thingSoC/TSOC_USBUART2/TSOC_USBUART2/documentation/pinout/TSOC_USBUART2_pinout.pdf

Sheet1

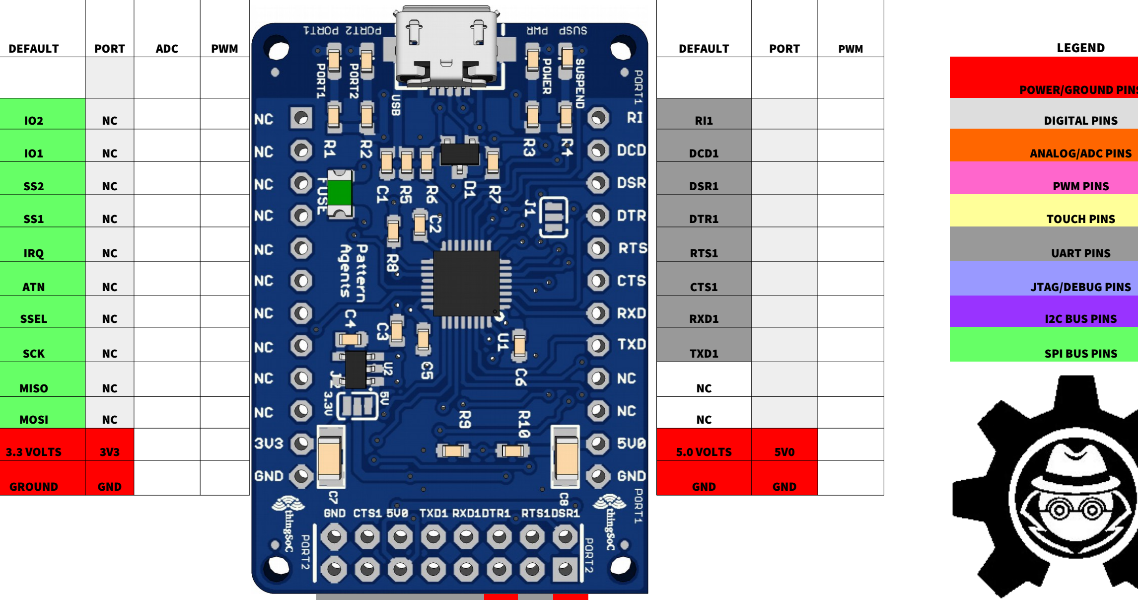
[picture p10: figure]
DIGITAL PINS; DCD1; ANALOG/ADC PINS; DSR1; PWM PINS; DTR1; TOUCH PINS; IRQ; RTS1; UART PINS; ATN; CTS1; JTAG/DEBUG PINS; SSEL; RXD1; I2C BUS PINS; SCK; TXD1; SPI BUS PINS; MISO; MOSI; 3.3 VOLTS; 5.0 VOLTS; GROUND; GND

Page 1

USB

DEFAULT | PORT | ADC | PWM | DEFAULT | PORT | PWM | LEGEND
| | | | | | | POWER/GROUND PINS

DSR2
RTS2

DTR2
TXD2

RXD2
5V0

CTS2
GND

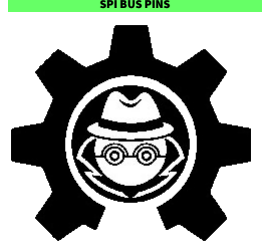
[picture p11: figure]

## PatternAgents thingSoC USBUART2

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
## http://github.com/thingsoc/usbuart2
