thingSoC/TSOC_USBUART2/TSOC_USBUART2/eagleUp/eagleUp_TSOC_USBUART2_board_bottom.jpg

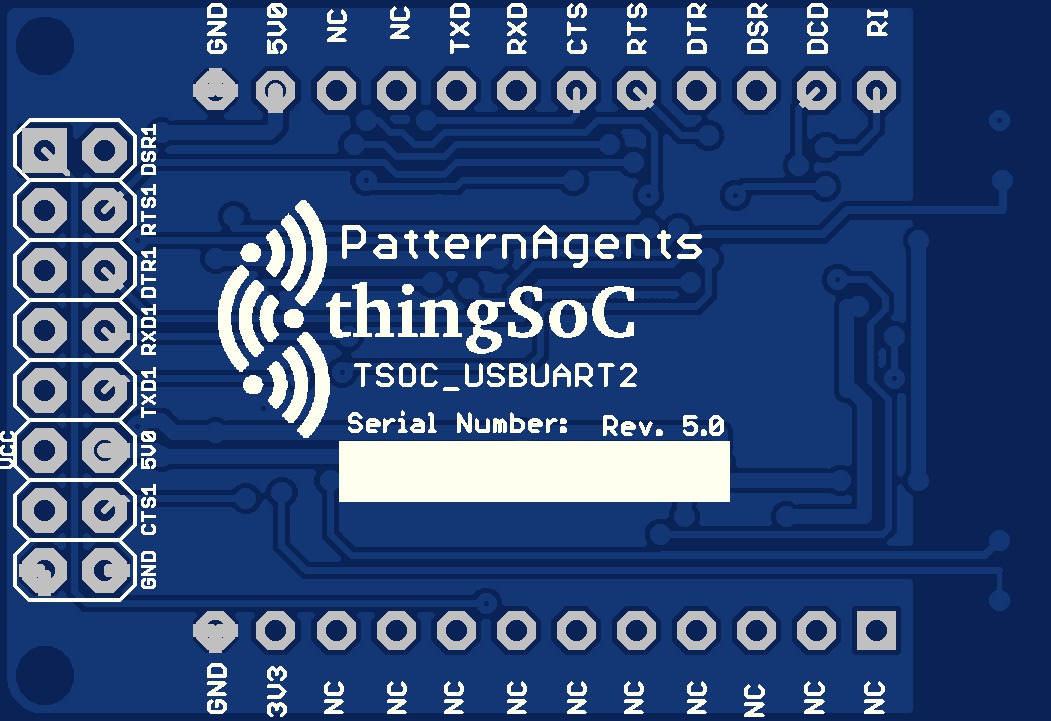
TSOC_USBUART2/eagleUp/eagleUp_TSOC_USBUART2_board_bottom.jpg
