thingSoC/TSOC_USBUART2/TSOC_USBUART2/eagleUp/eagleUp_TSOC_USBUART2_board_top.jpg

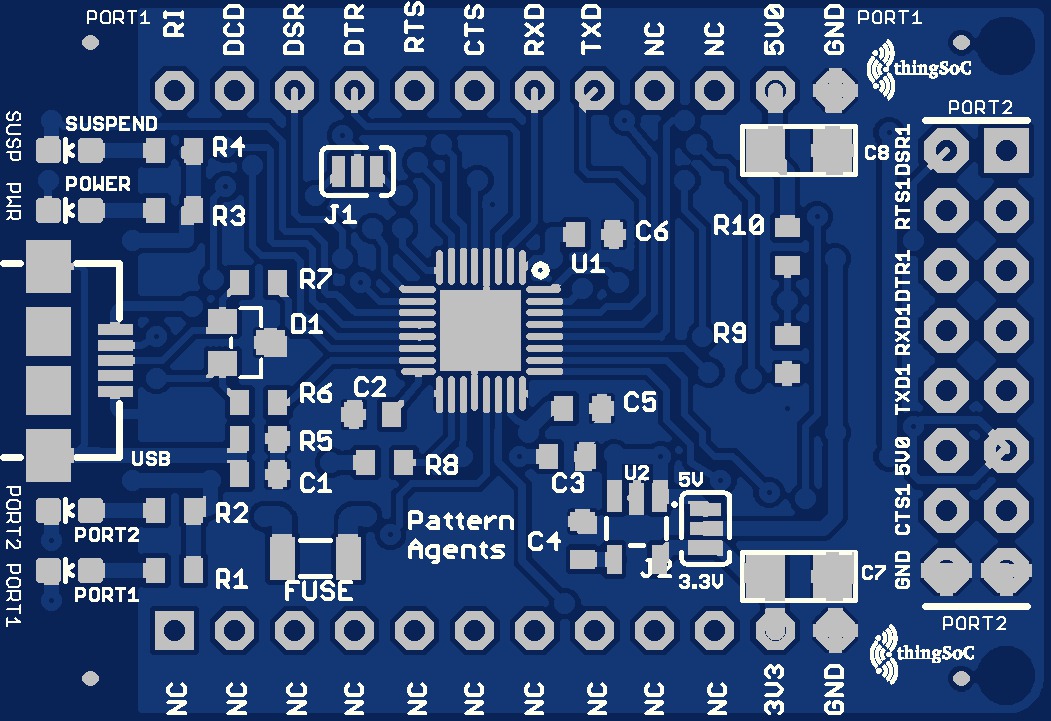
TSOC_USBUART2/eagleUp/eagleUp_TSOC_USBUART2_board_top.jpg
