thingSoC/TSOC_USBUART2/TSOC_USBUART2/images/product/TSOC_UART_top_pop.png

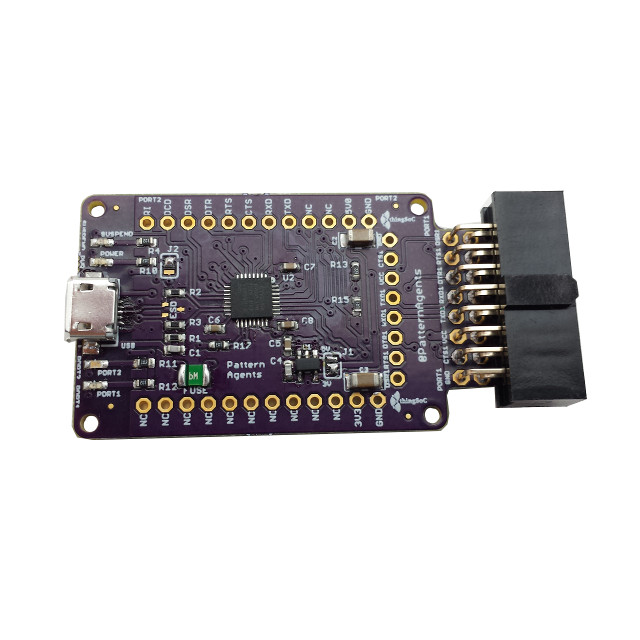
TSOC_USBUART2/images/product/TSOC_UART_top_pop.png
