thingSoC/TSOC_USBUART2/TSOC_USBUART2/images/product/TSOC_USBUART2_adapt_rs485_horiz.jpg

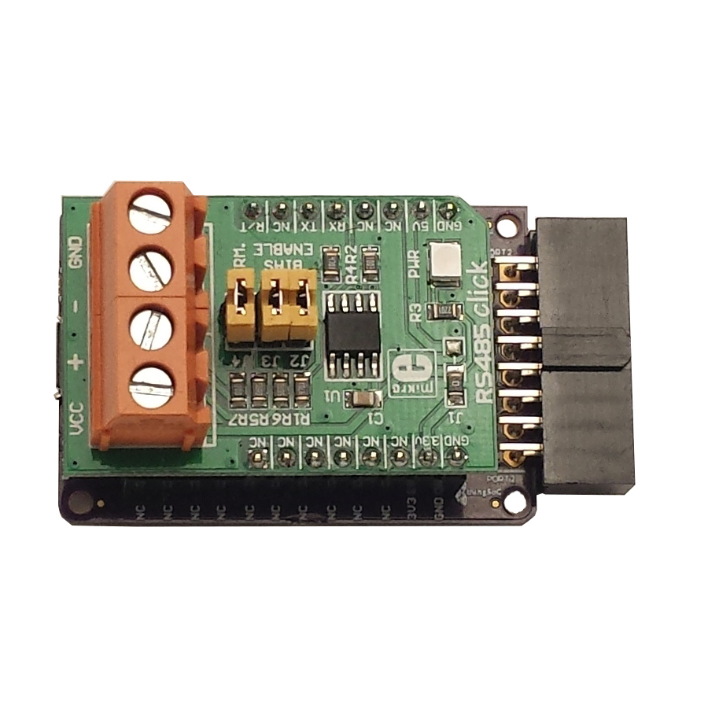
TSOC_USBUART2/images/product/TSOC_USBUART2_adapt_rs485_horiz.jpg
