thingSoC/TSOC_USBUART2/TSOC_USBUART2/images/product/TSOC_USBUART2_bot.png

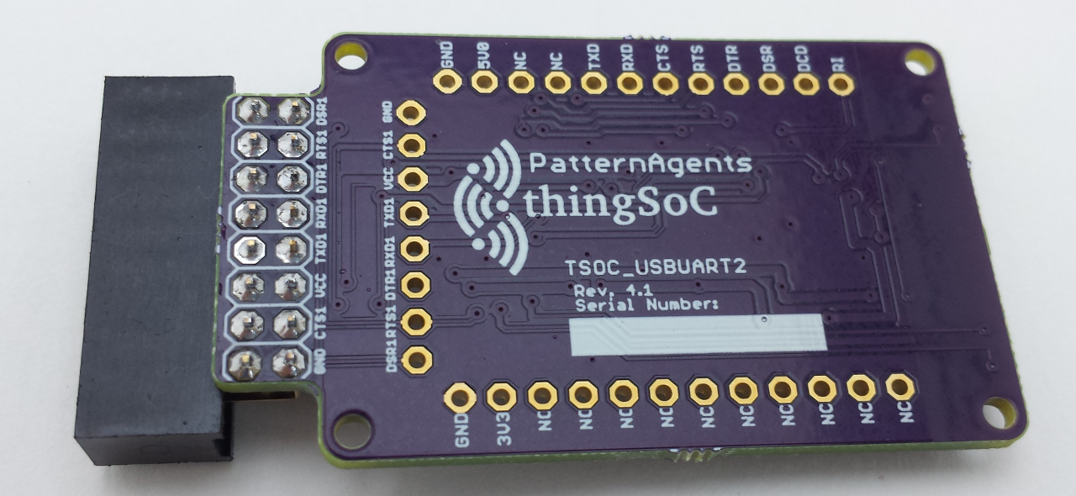
TSOC_USBUART2/images/product/TSOC_USBUART2_bot.png
