thingSoC/TSOC_USBUART2/TSOC_USBUART2/images/product/TSOC_USBUART2_prog_neoled2.png

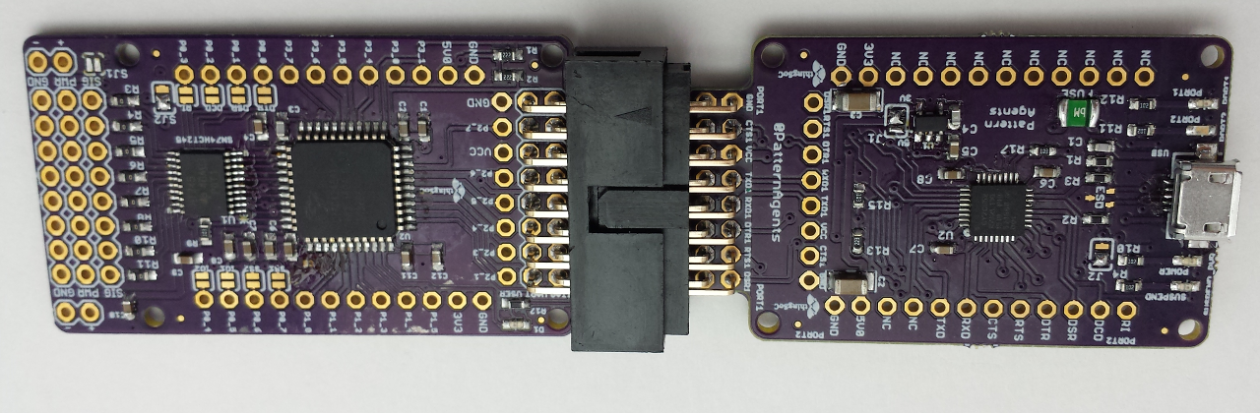
TSOC_USBUART2/images/product/TSOC_USBUART2_prog_neoled2.png
