thingSoC/TSOC_USBUART2/TSOC_USBUART2/images/product/TSOC_USBUART2_rails.png

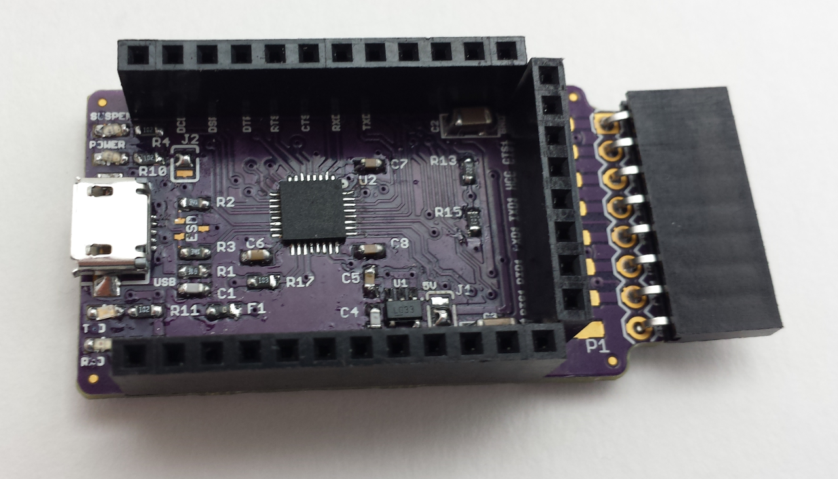
TSOC_USBUART2/images/product/TSOC_USBUART2_rails.png
