thingSoC/TSOC_USBUART2/TSOC_USBUART2/images/product/TSOC_USBUART2_top_pop_sqr.jpg

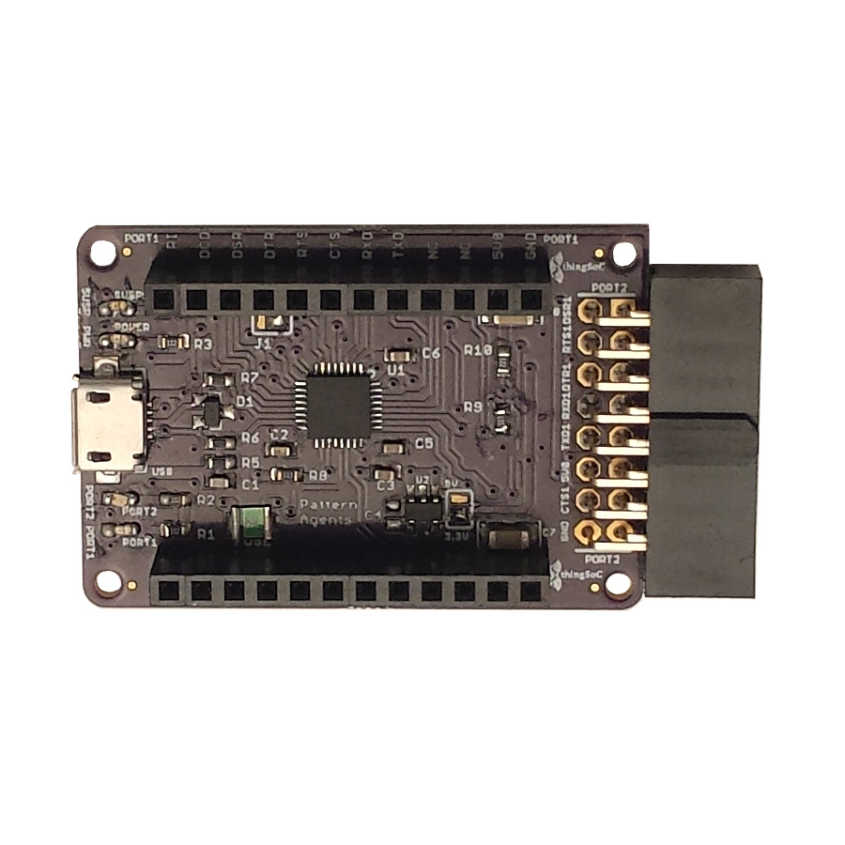
TSOC_USBUART2/images/product/TSOC_USBUART2_top_pop_sqr.jpg
