thingSoC/TSOC_USBUART2/TSOC_USBUART2/images/product/TSOC_USBUART2_with_ESP32S.png

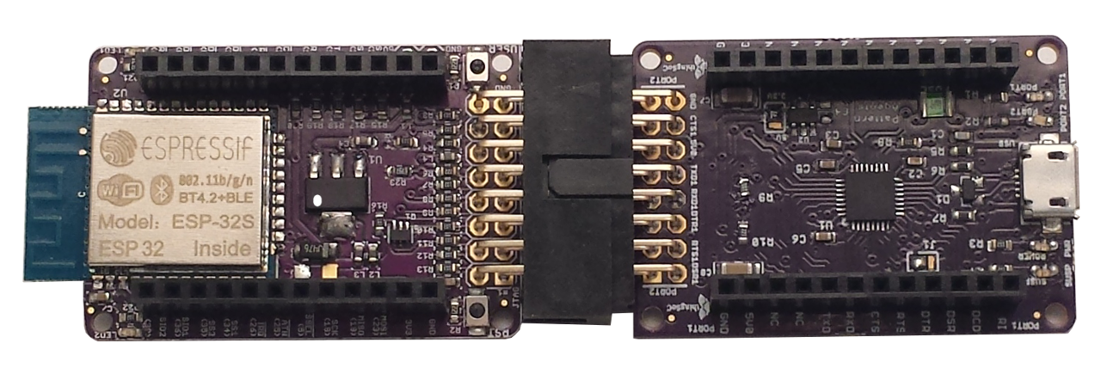
TSOC_USBUART2/images/product/TSOC_USBUART2_with_ESP32S.png
