thingSoC/TSOC_USBUART2/TSOC_USBUART2/images/TSOC_USBUART2.png

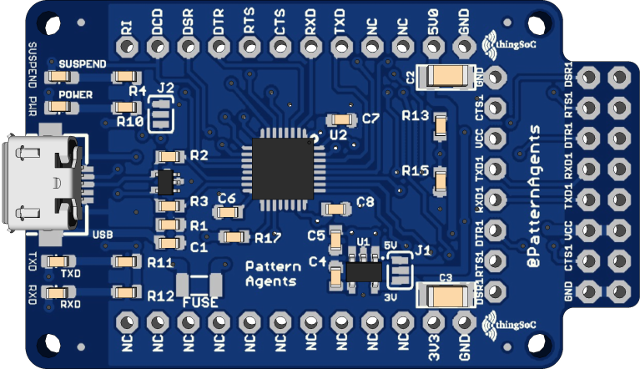
TSOC_USBUART2/images/TSOC_USBUART2.png
