thingSoC/TSOC_USBUART2/TSOC_USBUART2/images/TSOC_USBUART2_iso.png

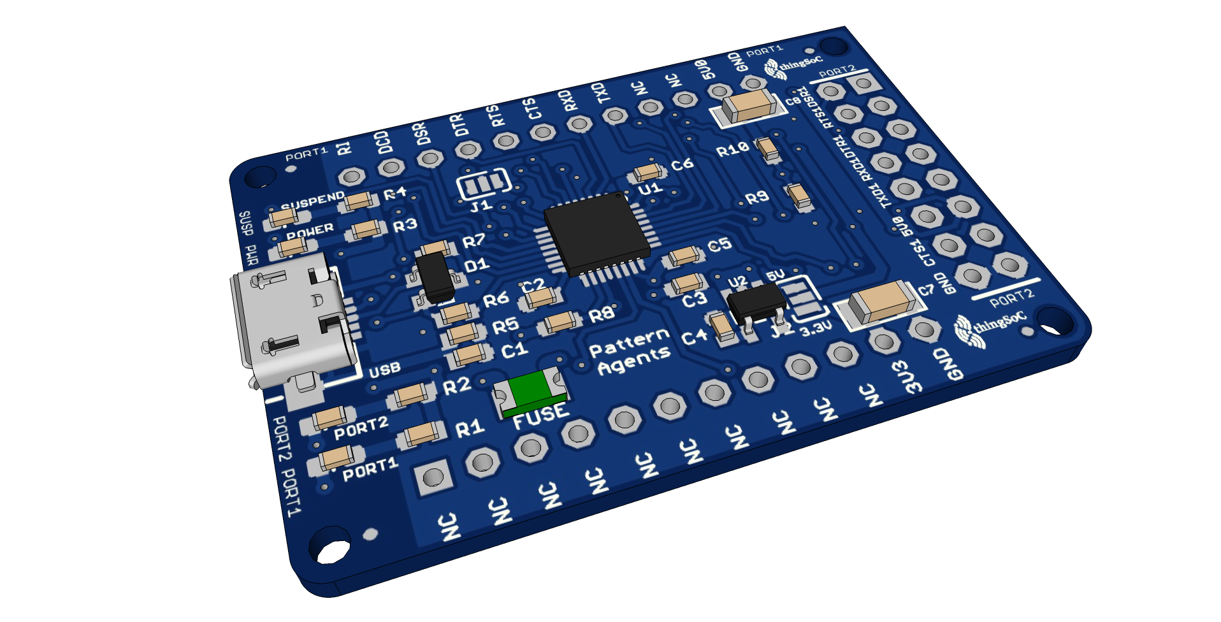
TSOC_USBUART2/images/TSOC_USBUART2_iso.png
