thingSoC/TSOC_USBUART2/TSOC_USBUART2/images/TSOC_USBUART2_top_vert.png

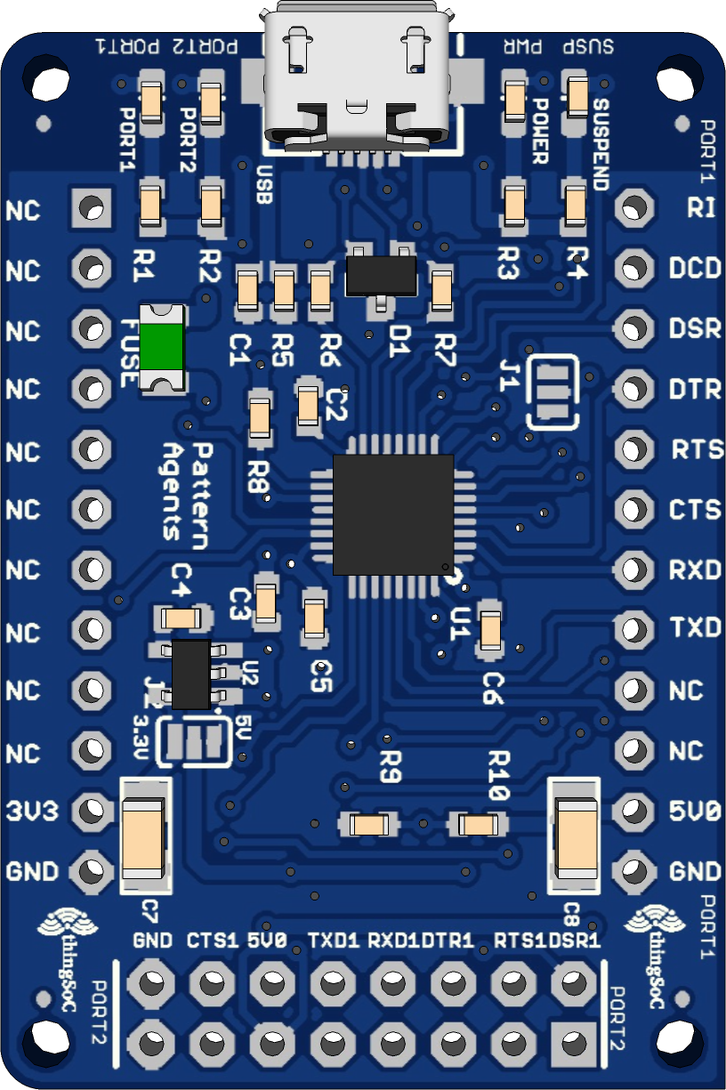
TSOC_USBUART2/images/TSOC_USBUART2_top_vert.png
