thingSoC/TSOC_USBUART2/TSOC_USBUART2/revisions/R4_0/TSOC_USBUART2_sch_blk.pdf

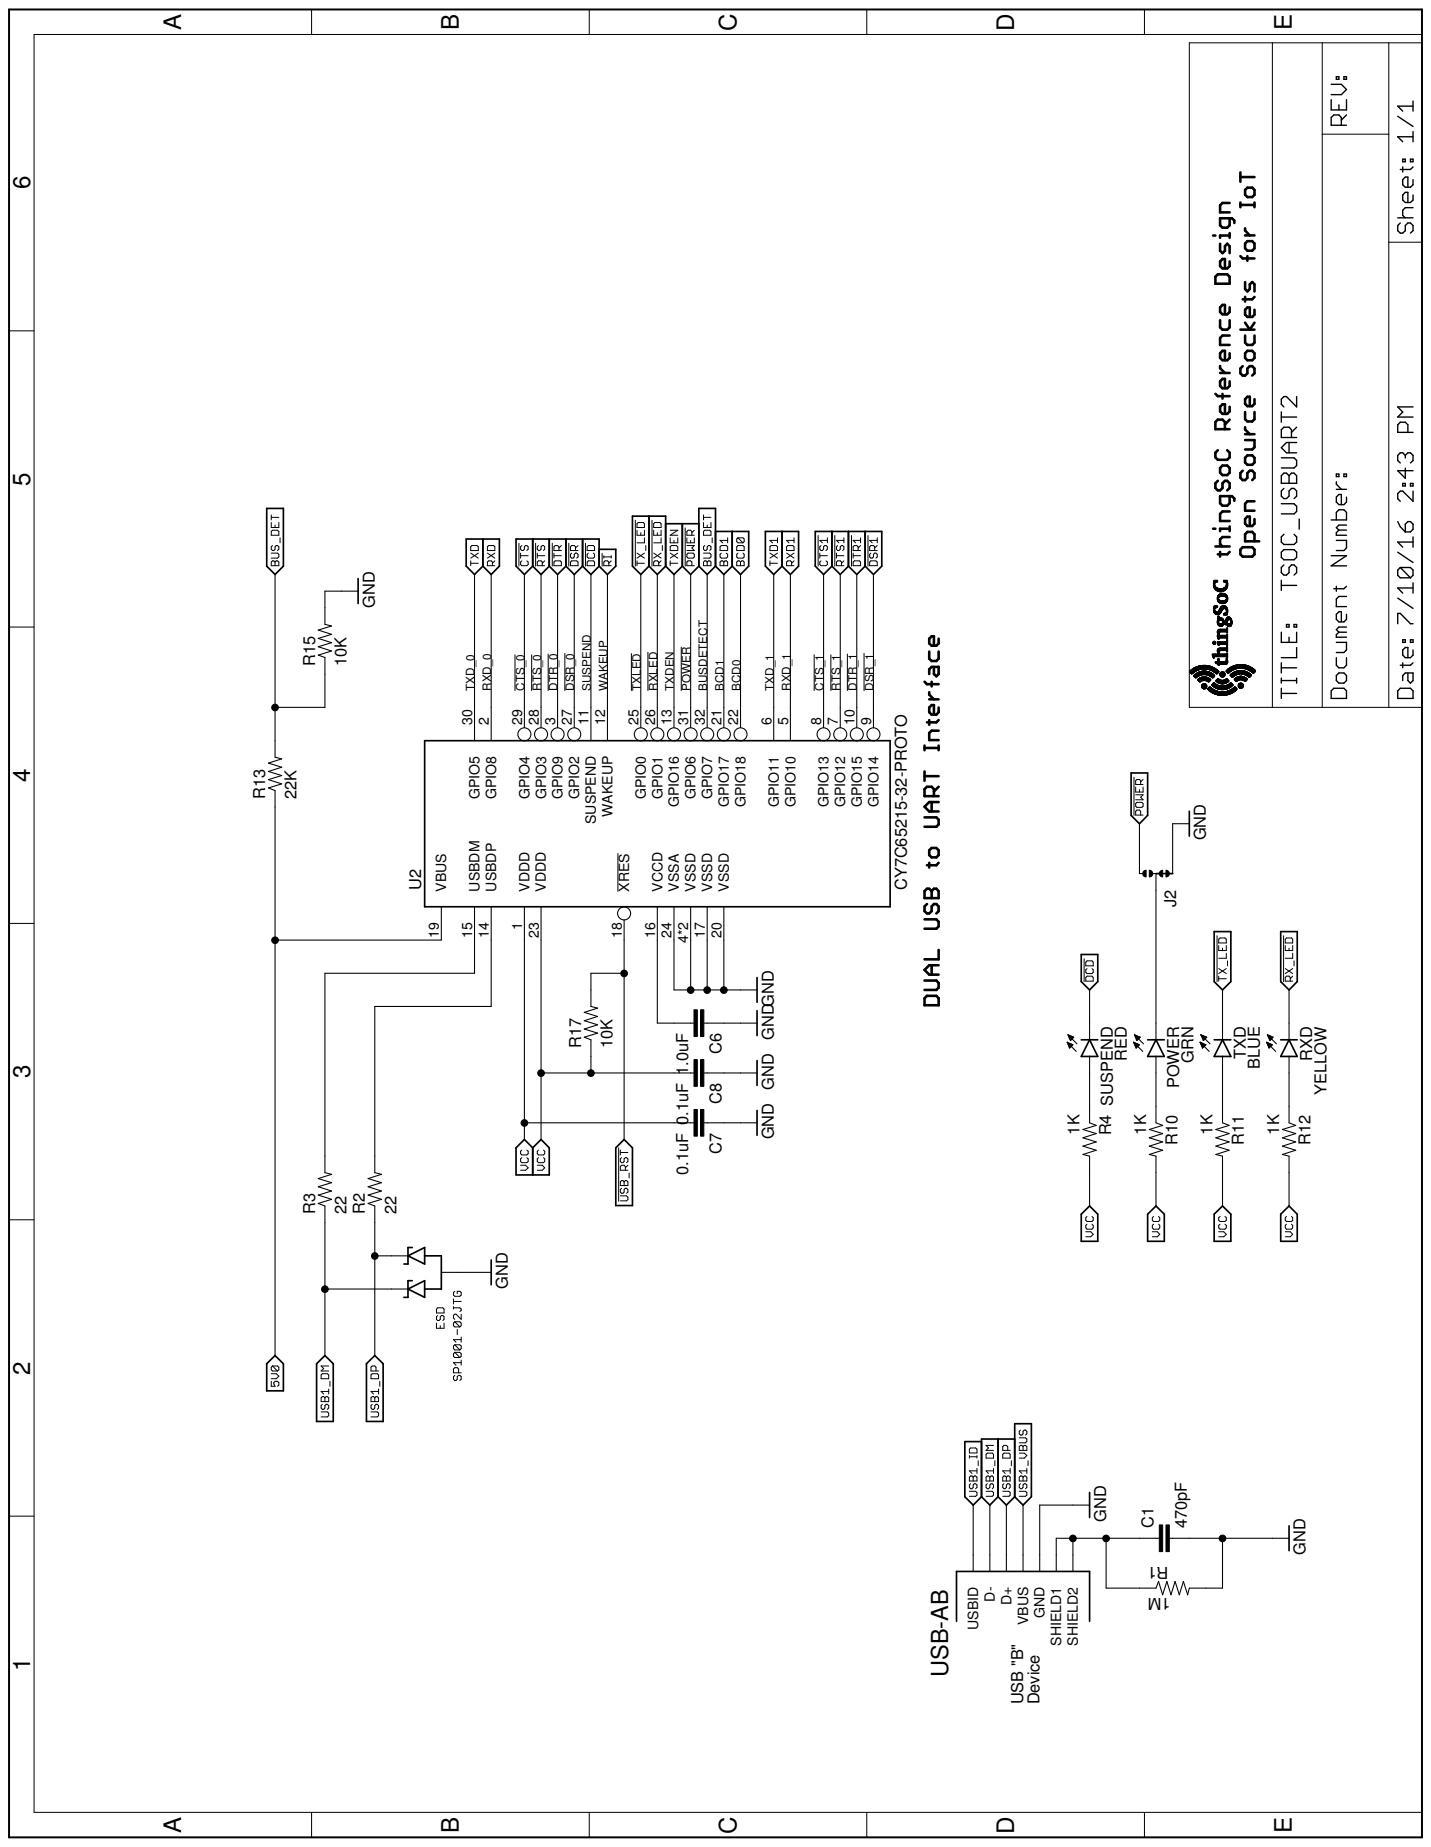
[picture p45: page 1]

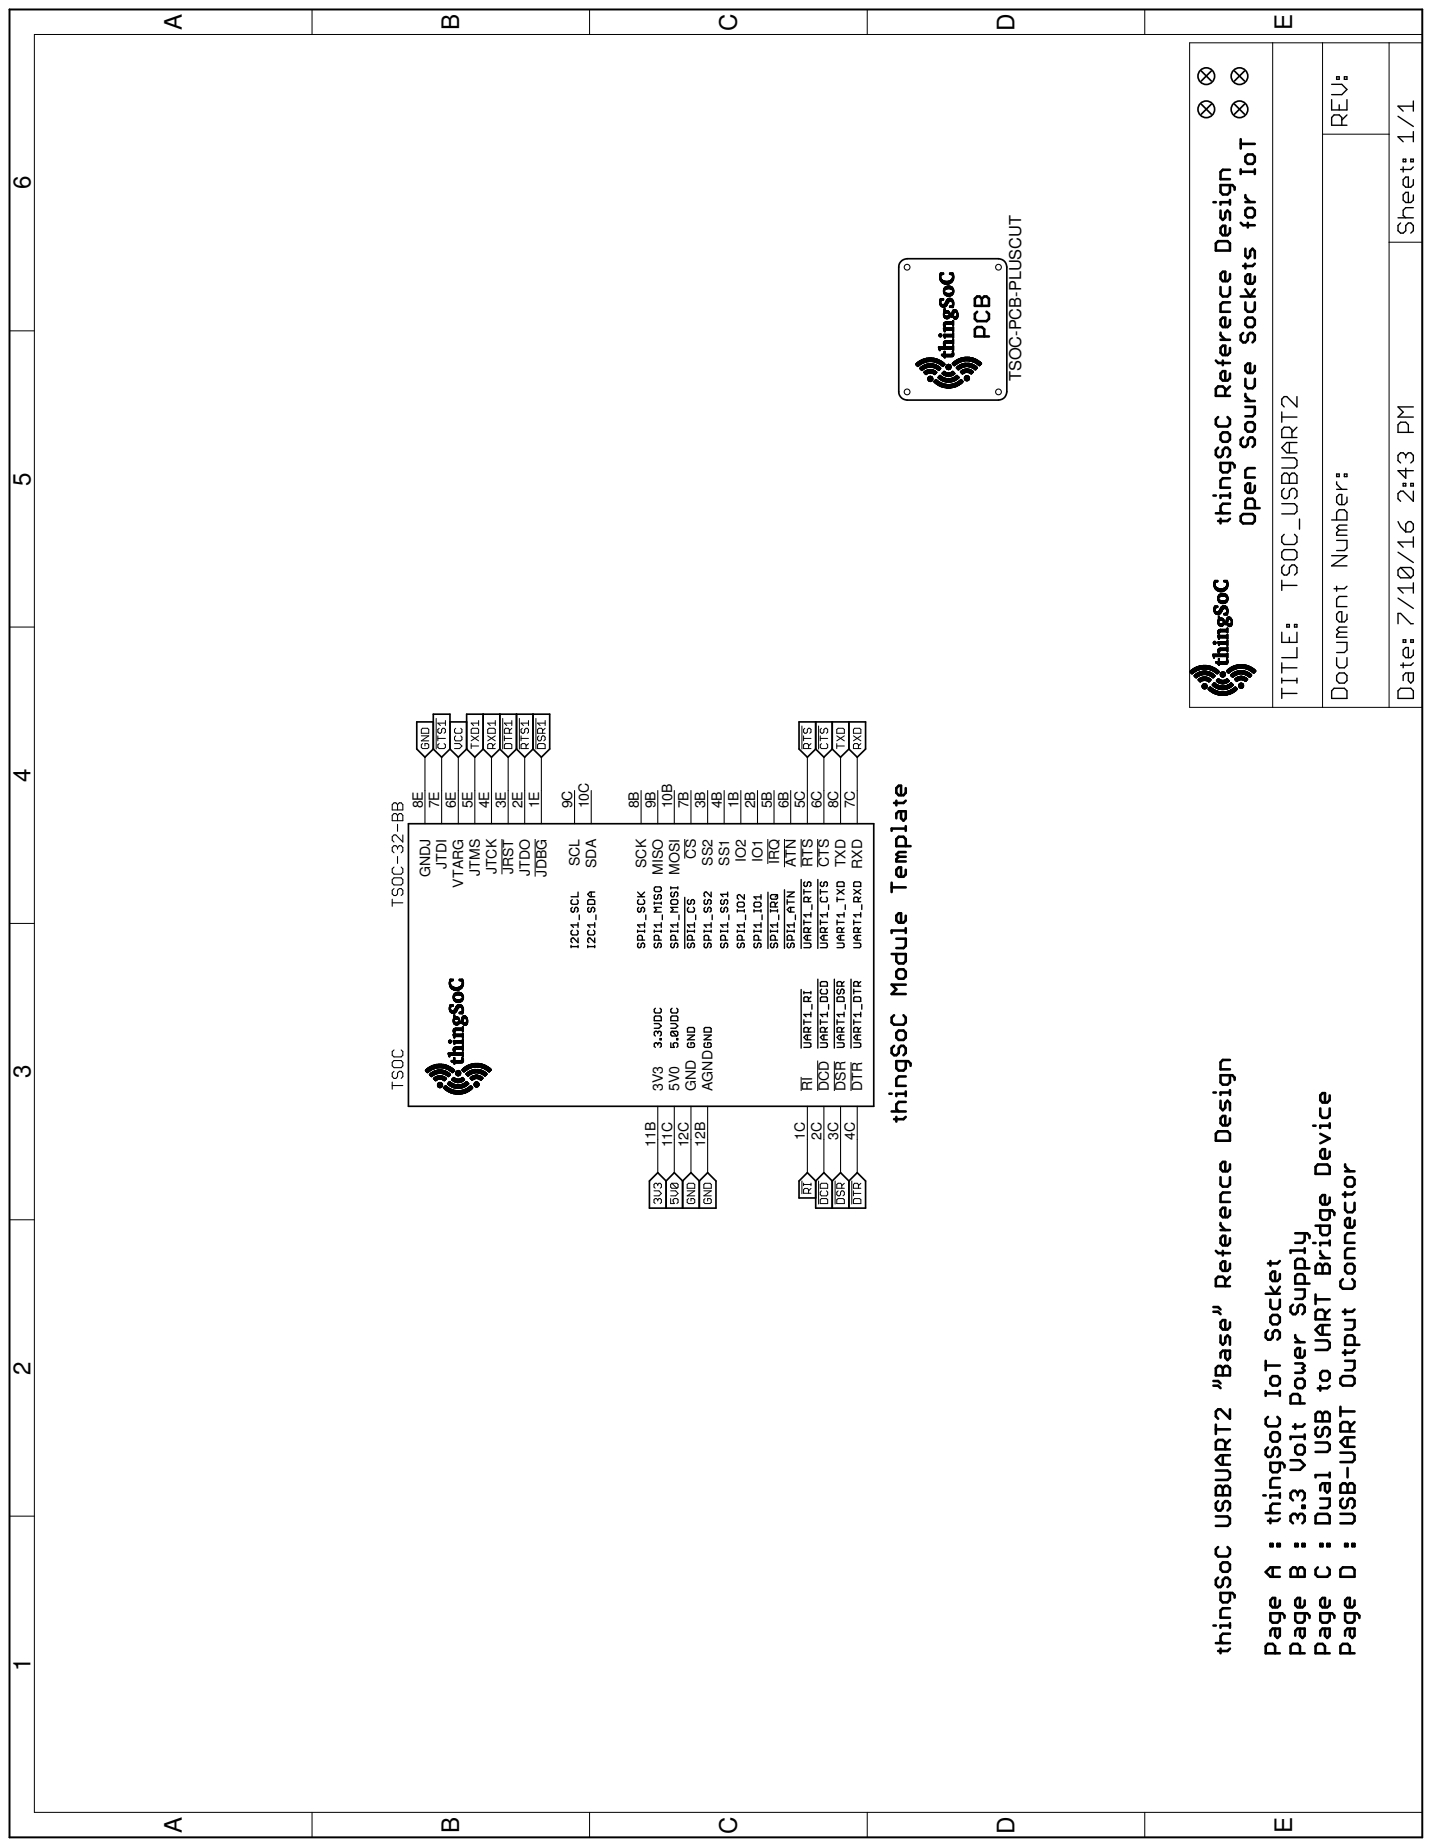
[picture p46: page 2]

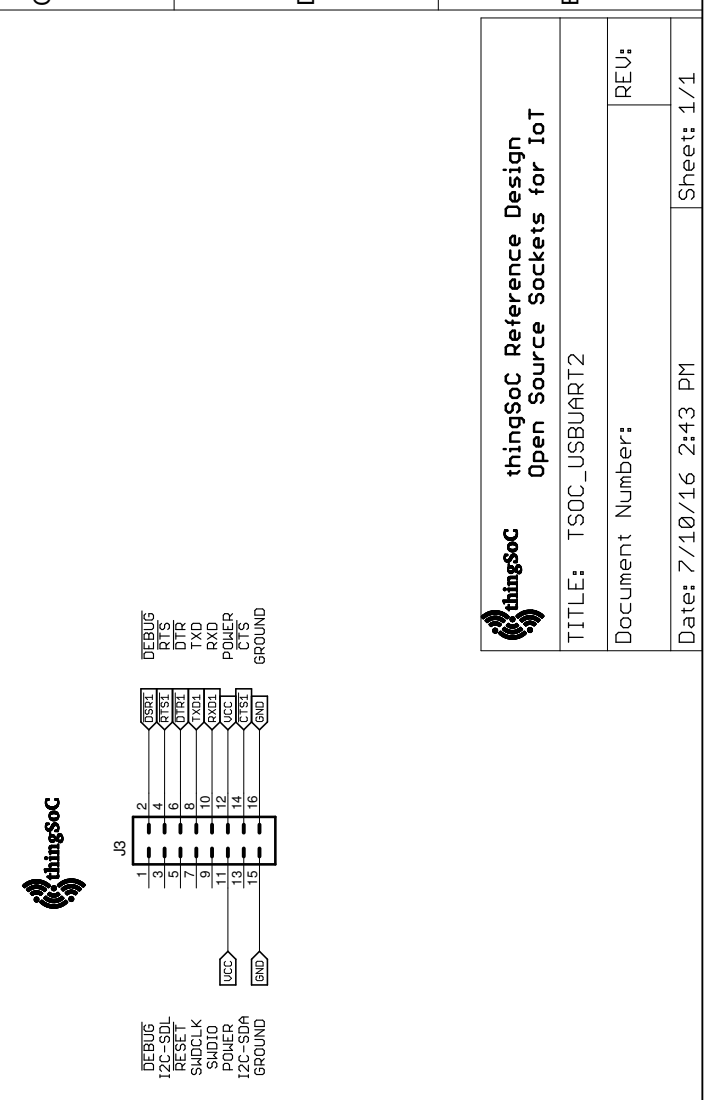
[picture p47: page 3]

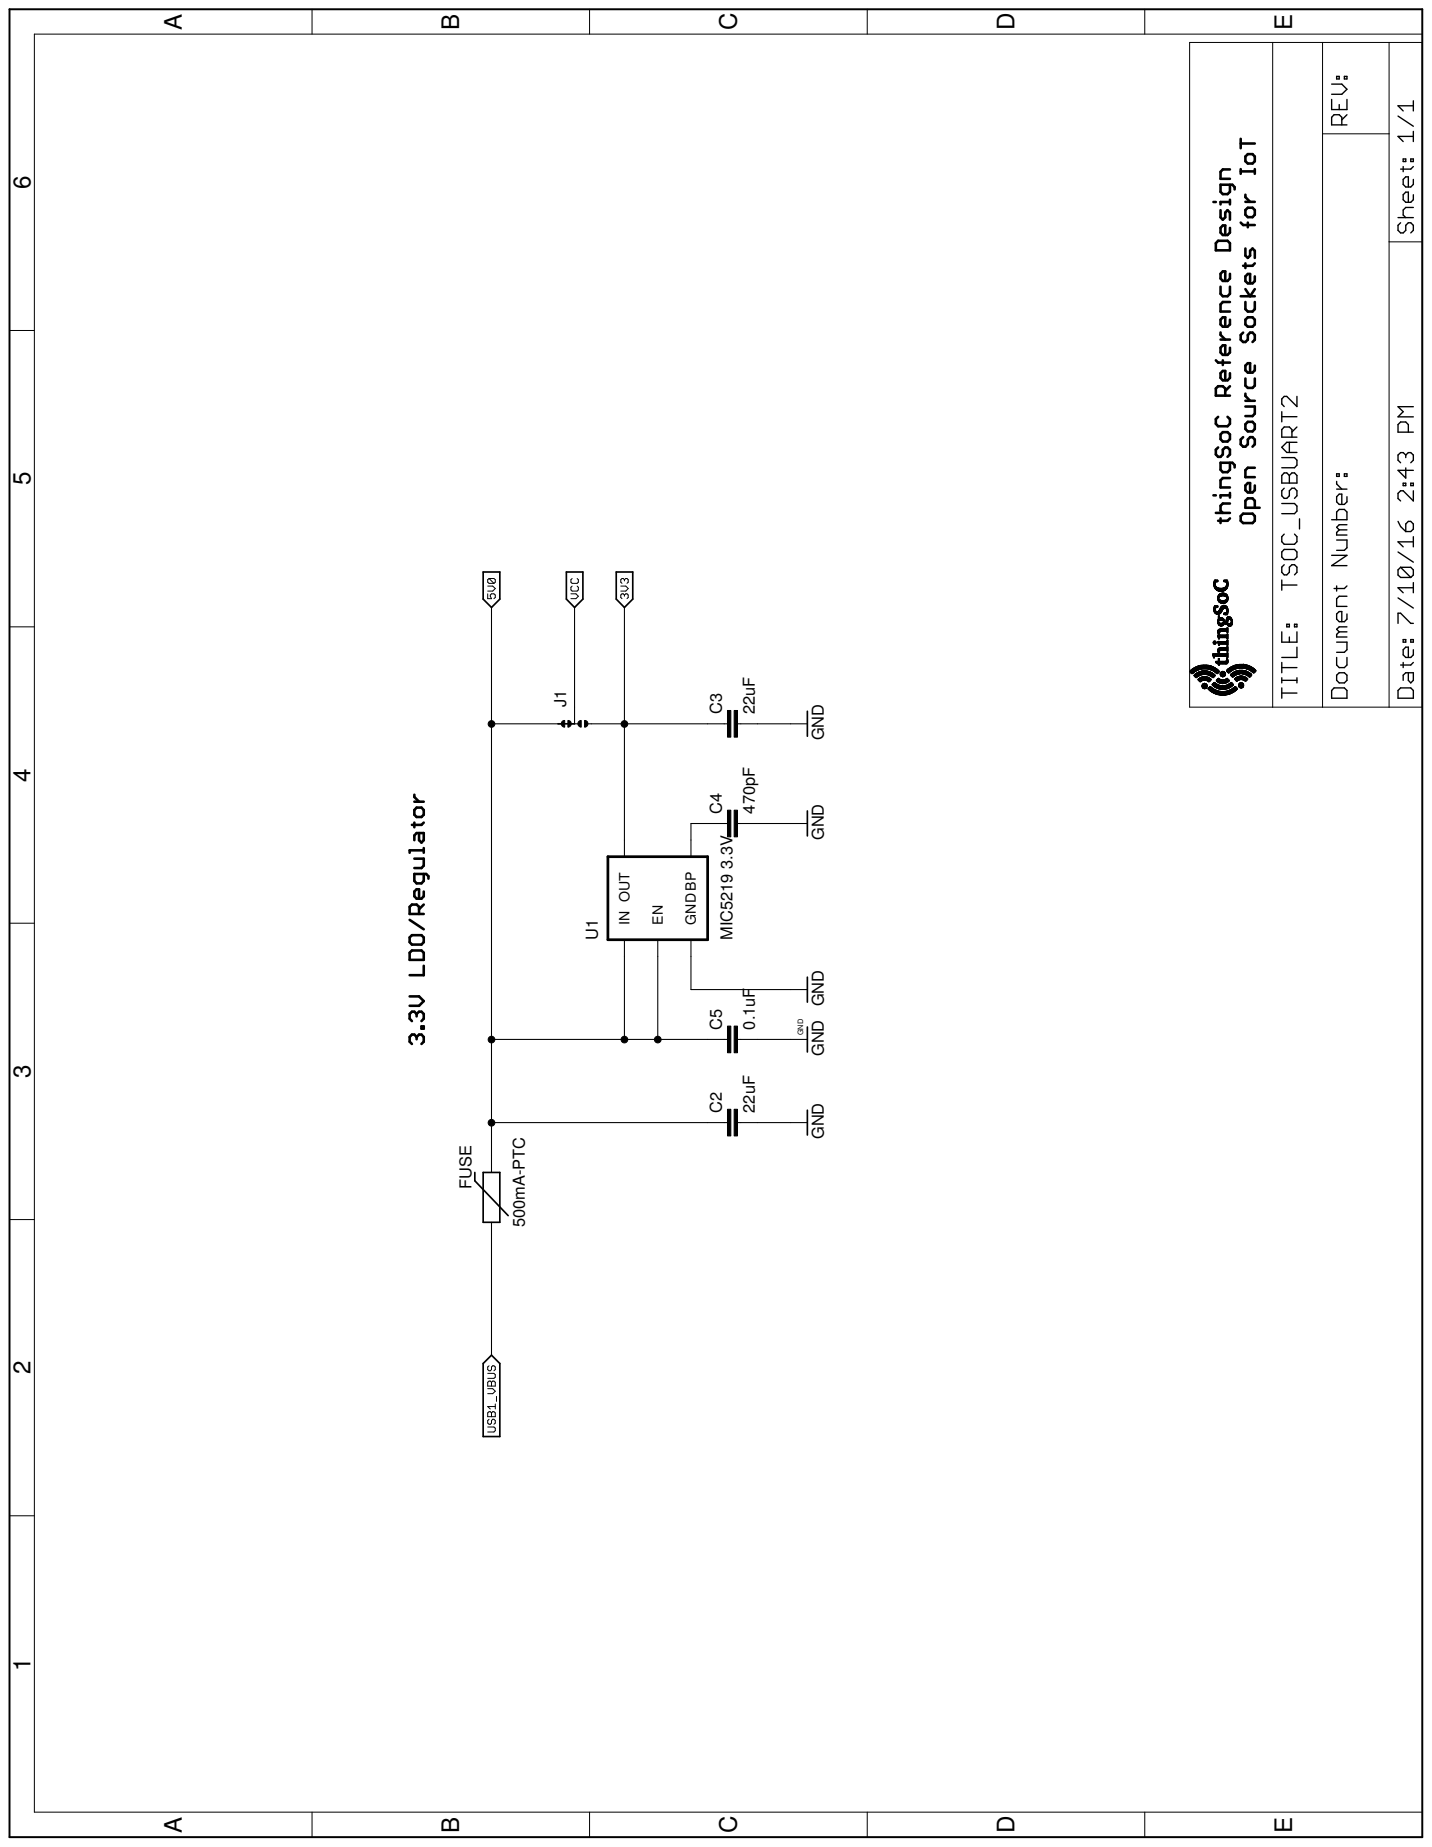
[picture p48: page 4]

GNDGND 470pF M1 GND 1.0uFGND 10K 22K 0.1uF 0.1uF GND GND 2222 GND 10K GND GRN 1K BLUE 1K YELLOW 1K RED 1K MIC5219 3.3VGND GND 470pF 0.1uF GND GND GND CY7C65215-32-PROTO GND 22uF 22uF TSOC-PCB-PLUSCUT 500mA-PTC D+D- VBUS GND USBID SHIELD1 SHIELD2 C1 1 R C6R17 R13 C8 C7 R3 R2 R15 ATN 6B RI 1C DCD 2C DSR 3C DTR 4C TXD 8C IO2 1B IO1 2B RTS 5C CTS 6C IRQ 5B SS2 3B SS1 4B CS 7B MOSI 10B MISO 9B SCK 8B GND 12C AGND 12B 3V3 11B RXD 7C SDA 10C SCL 9C 5V0 11C JDBG 1E JTDO 2E JRST 3E JTCK 4E JTMS 5E VTARG 6E JTDI 7E GNDJ 8E POWER R10 TXD R11 RXD R12 SUSPEND R4 U1INGNOD UT EN BP C4 C5 U2 XRES 18 GPIO2 27 SUSPEND 11 WAKEUP 12 VCCD 16 USBDM 15 USBDP 14 VSSD 4*2 VSSD 17 VSSD 20 GPIO5 30 GPIO8 2 VDDD 1 VSSA 24 VBUS 19 GPIO0 25 GPIO1 26 GPIO3 28 GPIO4 29 GPIO9 3 GPIO6 31 GPIO7 32 GPIO17 21 GPIO18 22 GPIO10 5 GPIO11 6 GPIO14 9 GPIO12 7 GPIO13 8 GPIO15 10 VDDD 23 GPIO16 13 J1 J2 C2 C3 J3 1 2 3 4 5 6 7 8 9 10 11 12 13 14 15 16 FUSE ABCDE ABCDE 1 2 3 4 5 6 ABCDE ABCDE 1 2 3 4 5 6 ABCDE ABCDE 1 2 3 4 5 6 USB-AB ABCDE ABCDE 1 2 3 4 5 6 GND TXLED RXLED POWER BCD1 BCD0 BUSDETECT WAKEUP TXD_0 RXD_0 CTS_0 RTS_0 DTR_0 DSR_0 SUSPEND TXD_1 RXD_1 CTS_1 RTS_1 DTR_1 DSR_1 TXDEN USB "B" Device
