thingSoC/TSOC_USBUART2/TSOC_USBUART2/revisions/R4_0/TSOC_USBUART2_bsilk.pdf

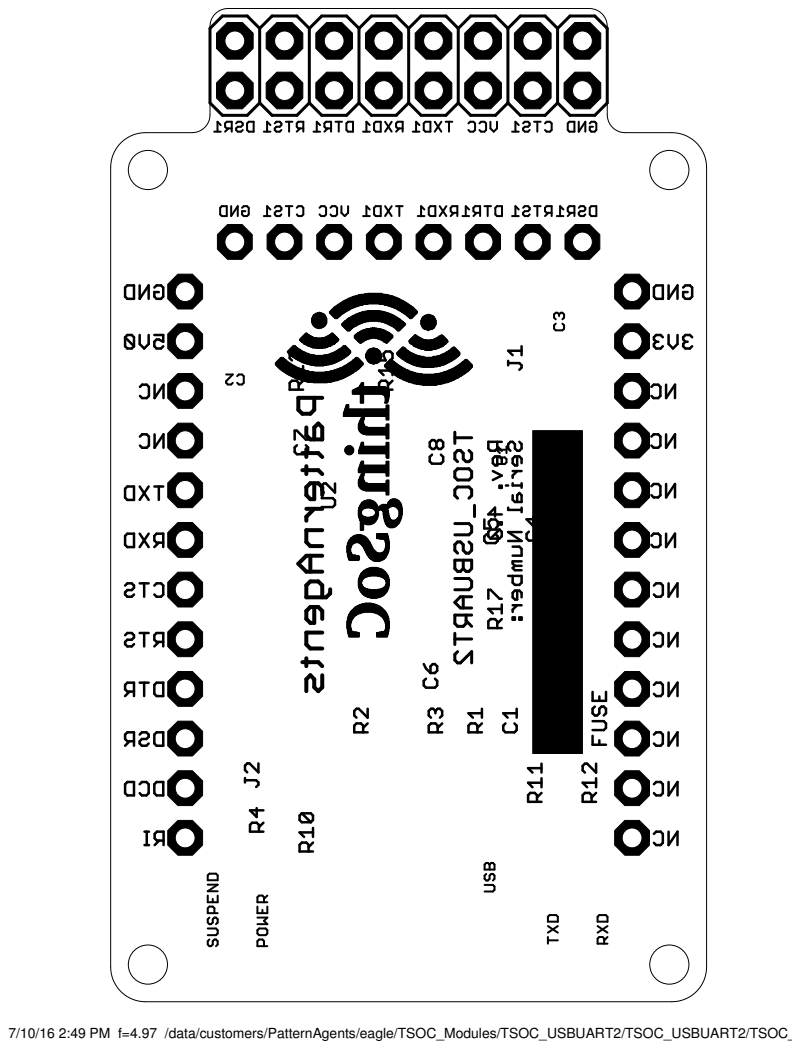
[picture p73: page 1]

7/10/16 2:49 PM f=4.97 /data/customers/PatternAgents/eagle/TSOC_Modules/TSOC_USBUART2/TSOC_USBUART2/TSOC_USBUART2.brd
