thingSoC/TSOC_USBUART2/TSOC_USBUART2/revisions/R4_1/TSOC_USBUART2_assembly.pdf

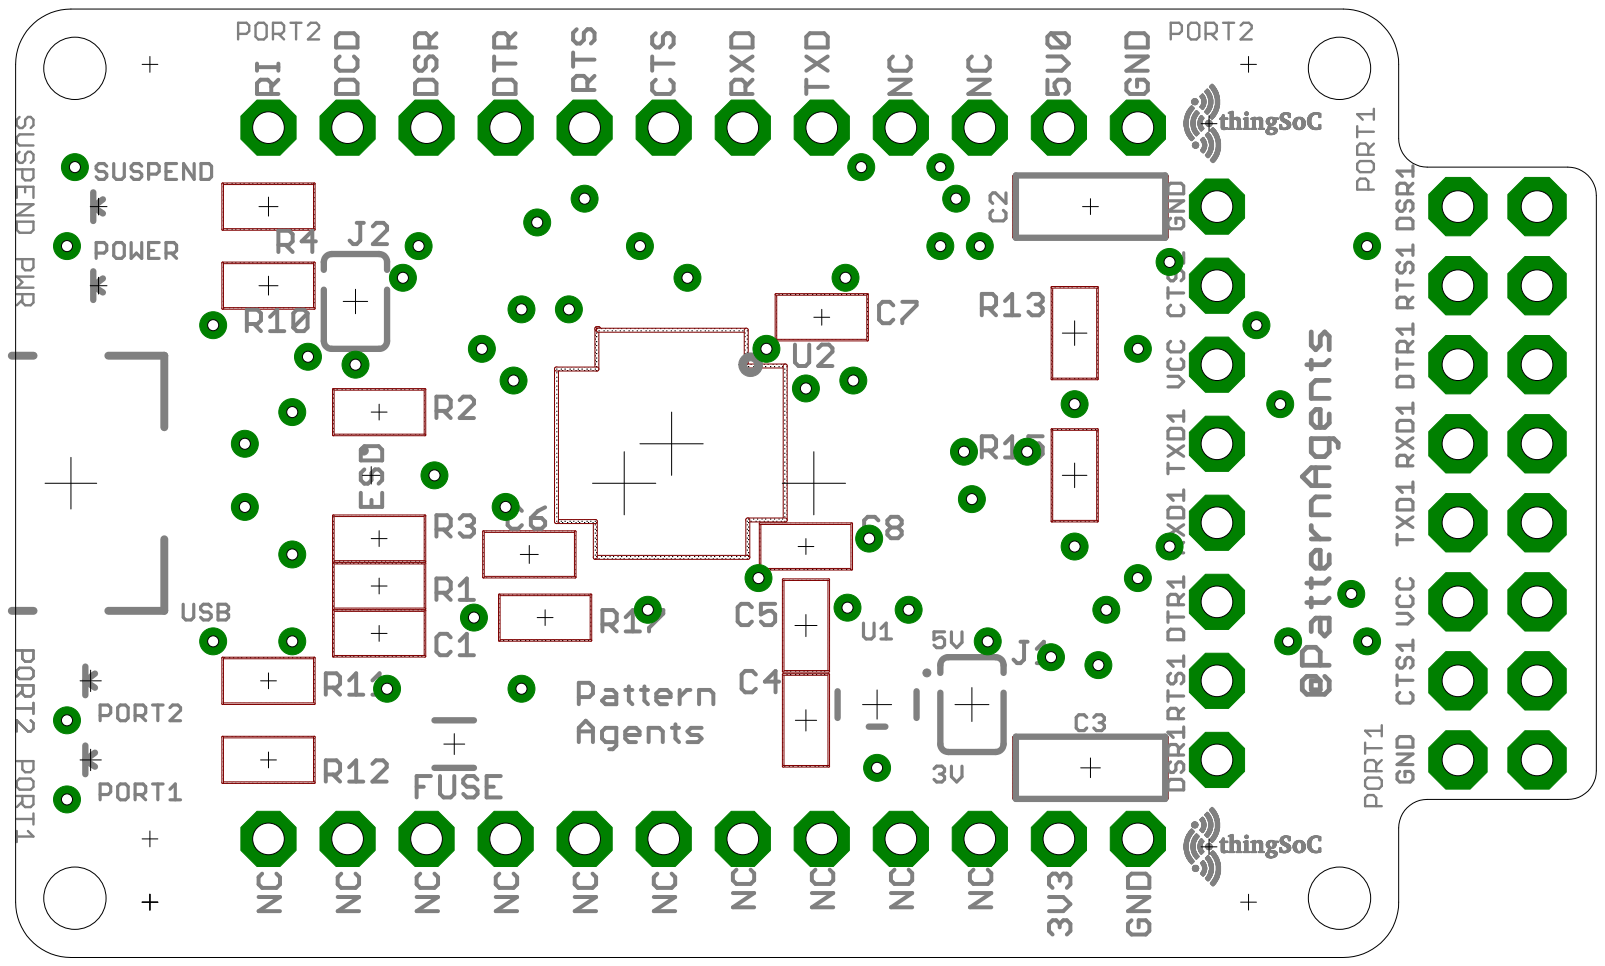
[picture p74: page 1]
