thingSoC/TSOC_USBUART2/TSOC_USBUART2/revisions/R4_0/TSOC_USBUART2_assembly.pdf

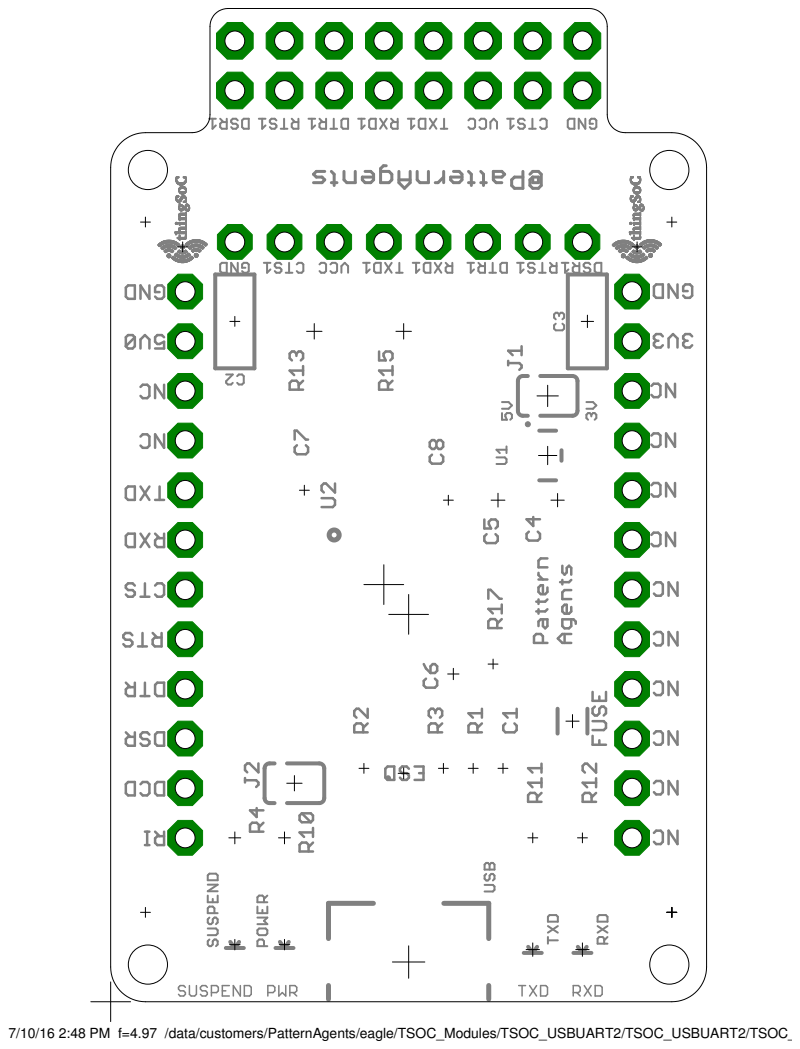
[picture p75: page 1]

7/10/16 2:48 PM f=4.97 /data/customers/PatternAgents/eagle/TSOC_Modules/TSOC_USBUART2/TSOC_USBUART2/TSOC_USBUART2.brd
